Dejv29/arduino-esp8266-amplifier-controller/images/IMG_20260223_130729.jpg

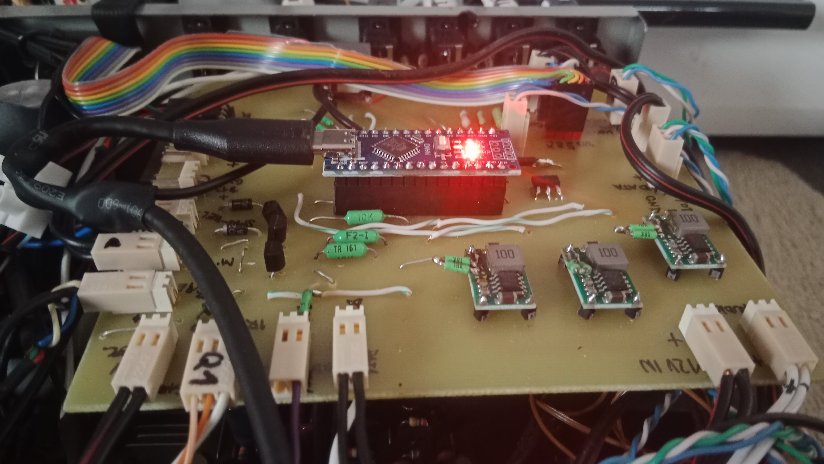
images/IMG_20260223_130729.jpg
