Dejv29/arduino-esp8266-amplifier-controller/images/IMG_20260223_130744.jpg

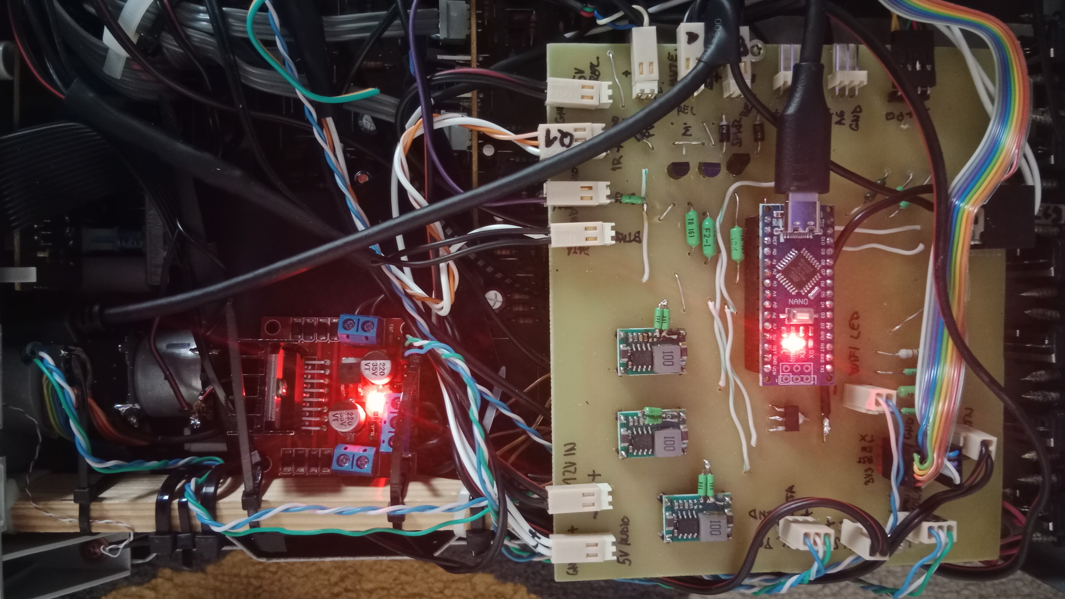
images/IMG_20260223_130744.jpg
